aadabathon/SFPmodule/Docs/SFPibpptr06-06.pdf

# SFP Example from Wikipedia…

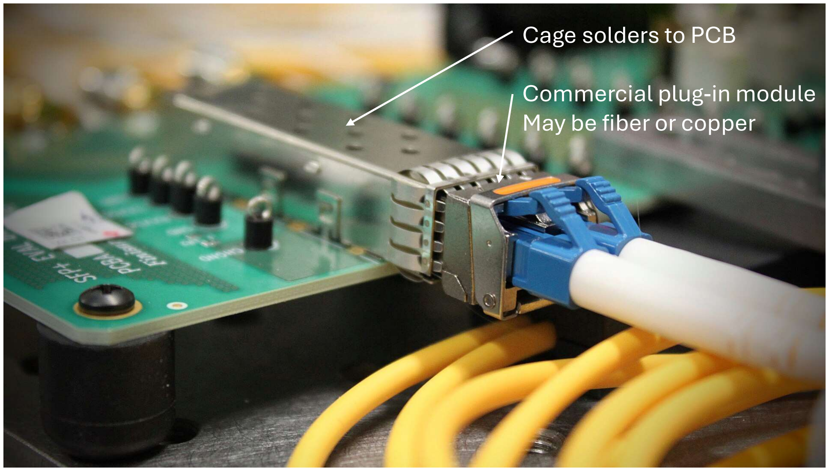
[picture p22: figure]
Cage solders to PCB; Commercial plug-in module May be fiber or copper

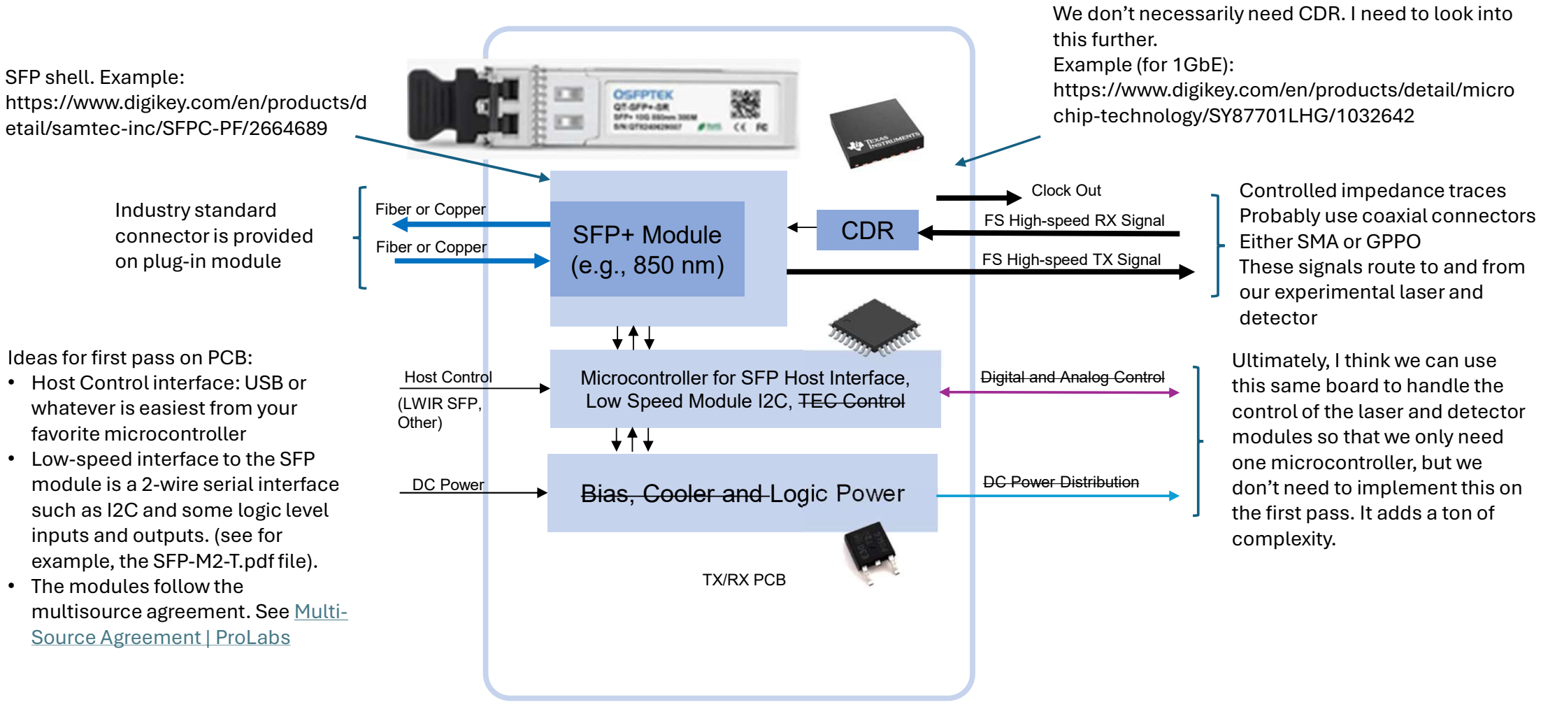
[picture p23: figure]
SFP+ Module (e.g., 850 nm); Microcontroller for SFP Host Interface, Low Speed Module I2C, TEC Control; Bias, Cooler and Logic Power; CDR; TX/RX PCB; Fiber or Copper; FS High-speed RX Signal; (LWIR SFP, Other); DC Power; Host Control; FS High-speed TX Signal; Digital and Analog Control; DC Power Distribution; Controlled impedance traces Probably use coaxial connectors Either SMA or GPPO These signals route to and from our experimental laser and detector; this further. Example (for 1GbE): https://www.digikey.com/en/products/detail/micro chip-technology/SY87701LHG/1032642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

We don’t necessarily need CDR. I need to look into

Ideas for first pass on PCB: • Host Control interface: USB or

favorite microcontroller • Low-speed interface to the SFP

example, the SFP-M2-T.pdf file). • The modules follow the
