aadabathon/SFPmodule/Screenshots/mk1_setup.png

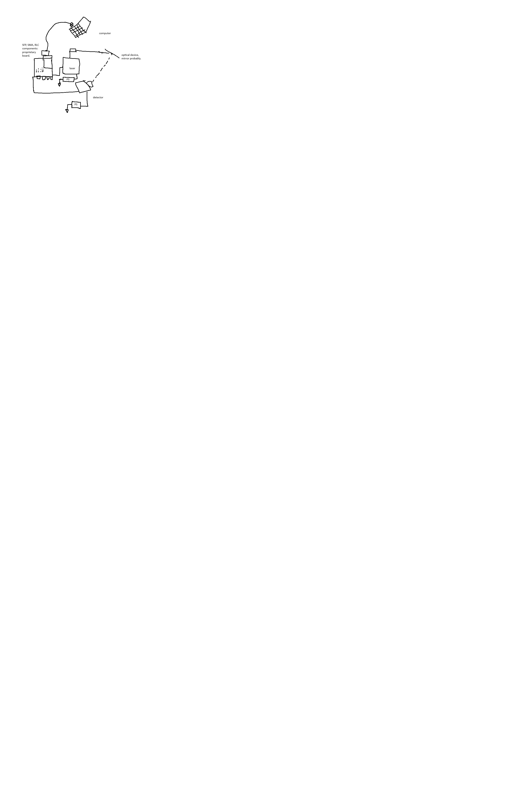
Screenshots/mk1_setup.png
